go4retro/c-key/src/ps2.h

/*
    C=Key - Commodore <-> PS/2 Interface
    Copyright Jim Brain and RETRO Innovations, 2004-2012

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
    ps2.h: public functions and KEY definitions

*/

#ifndef PS2_H
#define PS2_H

typedef enum { PS2_MODE_DEVICE = 1, PS2_MODE_HOST = 2 } ps2mode_t;

#define PS2_KEY_UP            0xf0
#define PS2_KEY_EXT           0xe0
#define PS2_KEY_EXT_2         0xe1


// normal keys
#define PS2_KEY_F9            0x01
#define PS2_KEY_F5            0x03
#define PS2_KEY_F3            0x04
#define PS2_KEY_F1            0x05
#define PS2_KEY_F2            0x06
#define PS2_KEY_F12           0x07
#define PS2_KEY_F10           0x09
#define PS2_KEY_F8            0x0a
#define PS2_KEY_F6            0x0b
#define PS2_KEY_F4            0x0c
#define PS2_KEY_TAB           0x0d
#define PS2_KEY_BACKQUOTE     0x0e
#define PS2_KEY_ALT           0x11
#define PS2_KEY_LSHIFT        0x12
#define PS2_KEY_LCTRL         0x14
#define PS2_KEY_Q             0x15
#define PS2_KEY_1             0x16
#define PS2_KEY_Z             0x1a
#define PS2_KEY_S             0x1b
#define PS2_KEY_A             0x1c
#define PS2_KEY_W             0x1d
#define PS2_KEY_2             0x1e
#define PS2_KEY_C             0x21
#define PS2_KEY_X             0x22
#define PS2_KEY_D             0x23
#define PS2_KEY_E             0x24
#define PS2_KEY_4             0x25
#define PS2_KEY_3             0x26
#define PS2_KEY_SPACE         0x29
#define PS2_KEY_V             0x2a
#define PS2_KEY_F             0x2b
#define PS2_KEY_T             0x2c
#define PS2_KEY_R             0x2d
#define PS2_KEY_5             0x2e
#define PS2_KEY_N             0x31
#define PS2_KEY_B             0x32
#define PS2_KEY_H             0x33
#define PS2_KEY_G             0x34
#define PS2_KEY_Y             0x35
#define PS2_KEY_6             0x36
#define PS2_KEY_M             0x3a
#define PS2_KEY_J             0x3b
#define PS2_KEY_U             0x3c
#define PS2_KEY_7             0x3d
#define PS2_KEY_8             0x3e
#define PS2_KEY_COMMA         0x41
#define PS2_KEY_K             0x42
#define PS2_KEY_I             0x43
#define PS2_KEY_O             0x44
#define PS2_KEY_0             0x45
#define PS2_KEY_9             0x46
#define PS2_KEY_PERIOD        0x49
#define PS2_KEY_SLASH         0x4a
#define PS2_KEY_L             0x4b
#define PS2_KEY_SEMICOLON     0x4c
#define PS2_KEY_P             0x4d
#define PS2_KEY_MINUS         0x4e
#define PS2_KEY_APOSTROPHE    0x52
#define PS2_KEY_INT2          0x53
#define PS2_KEY_LBRACKET      0x54
#define PS2_KEY_EQUALS        0x55
#define PS2_KEY_CAPS_LOCK     0x58
#define PS2_KEY_RSHIFT        0x59
#define PS2_KEY_ENTER         0x5a
#define PS2_KEY_RBRACKET      0x5b
#define PS2_KEY_BACKSLASH     0x5d
#define PS2_KEY_INT1          0x61
#define PS2_KEY_BS            0x66
#define PS2_KEY_NUM_1         0x69
#define PS2_KEY_NUM_4         0x6b
#define PS2_KEY_NUM_7         0x6c
#define PS2_KEY_NUM_0         0x70
#define PS2_KEY_NUM_PERIOD    0x71
#define PS2_KEY_NUM_2         0x72
#define PS2_KEY_NUM_5         0x73
#define PS2_KEY_NUM_6         0x74
#define PS2_KEY_NUM_8         0x75
#define PS2_KEY_ESC           0x76
#define PS2_KEY_NUM_LOCK      0x77
#define PS2_KEY_F11           0x78
#define PS2_KEY_NUM_PLUS      0x79
#define PS2_KEY_NUM_3         0x7a
#define PS2_KEY_NUM_MINUS     0x7b
#define PS2_KEY_NUM_STAR      0x7c
#define PS2_KEY_NUM_9         0x7d
#define PS2_KEY_SCROLL_LOCK   0x7e
#define PS2_KEY_F7            0x83


// extended keys
#define PS2_KEY_RALT          0x11
#define PS2_KEY_ECTRL         0x12
#define PS2_KEY_RCTRL         0x14
#define PS2_KEY_NUM_SLASH     0x4a
#define PS2_KEY_NUM_ENTER     0x5a
#define PS2_KEY_END           0x69
#define PS2_KEY_CRSR_LEFT     0x6b
#define PS2_KEY_HOME          0x6c
#define PS2_KEY_INSERT        0x70
#define PS2_KEY_DELETE        0x71
#define PS2_KEY_CRSR_DOWN     0x72
#define PS2_KEY_CRSR_RIGHT    0x74
#define PS2_KEY_CRSR_UP       0x75
#define PS2_KEY_PAGE_DOWN     0x7a
#define PS2_KEY_PAGE_UP       0x7d

// significantly extended keys
// E012E07C
#define PS2_KEY_PRINT_SCREEN  0x7c
// E11477E1F014F077
#define PS2_KEY_PCTRL         0x14
#define PS2_KEY_PAUSE         0x77


#define PS2_CMD_LEDS          0xed
#define PS2_CMD_ECHO          0xee
#define PS2_CMD_SET_CODE_SET  0xf0
#define PS2_CMD_READ_ID       0xf2
#define PS2_CMD_SET_RATE      0xf3
#define PS2_CMD_ENABLE        0xf4
#define PS2_CMD_DISABLE       0xf5
#define PS2_CMD_DEFAULT       0xf6
#define PS2_CMD_RESEND        0xfe
#define PS2_CMD_RESET         0xff

#define PS2_CMD_ERROR         0x00
#define PS2_CMD_BAT           0xaa
#define PS2_CMD_ECHO_RESP     0xee
#define PS2_CMD_ACK           0xfa
#define PS2_CMD_BAT_FAILURE   0xfc
#define PS2_CMD_OVERFLOW      0xff

#define PS2_LED_SCROLL_LOCK   (1 << 0)
#define PS2_LED_NUM_LOCK      (1 << 1)
#define PS2_LED_CAPS_LOCK     (1 << 2)

#define PS2_MS_CMD_RESET      PS2_CMD_RESET
#define PS2_MS_CMD_RESEND     PS2_CMD_RESEND
#define PS2_MS_CMD_ACK        PS2_CMD_ACK
#define PS2_MS_CMD_REPORT     0xf4
#define PS2_MS_CMD_REPORTOFF  0xf5
#define PS2_MS_CMD_SET_SAMPLE 0xf3
#define PS2_MS_CMD_READ_ID    PS2_CMD_READ_ID
#define PS2_MS_CMD_READ_DATA  0xeb

#define PS2_RX_BUFFER_MASK   (_BV(PS2_RX_BUFFER_SHIFT) - 1)
#define PS2_TX_BUFFER_MASK   (_BV(PS2_TX_BUFFER_SHIFT) - 1)
/*
 * After a device sends a byte to host, it has to holdoff for a while
 * before doing anything else.  One KB I tested this is 2.14mS.
 */

/* PS2 Clock INT */
#if defined __AVR_ATmega8__ ||  defined __AVR_ATmega16__ || defined __AVR_ATmega32__ || defined __AVR_ATmega162__
#  define CLK_INTDR     MCUCR     // INT Direction Register
#  define CLK_INTCR     GICR      // INT Control Register
#  define CLK_INTFR     GIFR      // INT Flag Register
#  if PS2_CLK_PIN == _BV(PD3)
#    define CLK_ISC0      ISC10
#    define CLK_ISC1      ISC11
#    define CLK_INT       INT1
#    define CLK_INTF      INTF1
#    define CLK_INT_vect  INT1_vect
#  elif PS2_CLK_PIN == _BV(PD2)
#    define CLK_ISC0      ISC00
#    define CLK_ISC1      ISC01
#    define CLK_INT       INT0
#    define CLK_INTF      INTF0
#    define CLK_INT_vect  INT0_vect
#  else
#    error "Please define CLK INT Settings"
#  endif
#else
#  define CLK_INTDR     EICRA     // INT Direction Register
#  define CLK_INTCR     EIMSK     // INT Control Register
#  define CLK_INTFR     EIFR      // INT Flag Register
#  if PS2_CLK_PIN == _BV(PD3)
#    define CLK_ISC0      ISC10
#    define CLK_ISC1      ISC11
#    define CLK_INT       INT1
#    define CLK_INTF      INTF1
#    define CLK_INT_vect  INT1_vect
#  else
#    define CLK_ISC0      ISC00
#    define CLK_ISC1      ISC01
#    define CLK_INT       INT0
#    define CLK_INTF      INTF0
#    define CLK_INT_vect  INT0_vect
#  endif
#endif

/* PS2 Timer */
#if defined __AVR_ATmega8__

#  define PS2_TIMER_COMP_vect   TIMER2_COMP_vect
#  define PS2_OCR               OCR2
#  define PS2_TCNT              TCNT2
#  define PS2_TCCR1             TCCR2
#  define PS2_TCCR1_DATA        _BV(CS21)
#  define PS2_TCCR2             TCCR2
#  define PS2_TCCR2_DATA        _BV(WGM21)
#  define PS2_TIFR              TIFR
#  define PS2_TIFR_DATA         _BV(OCF2)
#  define PS2_TIMSK             TIMSK
#  define PS2_TIMSK_DATA        _BV(OCIE2)

#elif defined __AVR_ATmega28__ || defined __AVR_ATmega48__ || defined __AVR_ATmega88__ || defined __AVR_ATmega168__

#  define PS2_TIMER_COMP_vect   TIMER2_COMPA_vect
#  define PS2_OCR               OCR2A
#  define PS2_TCNT              TCNT2
#  define PS2_TCCR1             TCCR2B
#  define PS2_TCCR1_DATA        _BV(CS21)
#  define PS2_TCCR2             TCCR2A
#  define PS2_TCCR2_DATA        _BV(WGM21)
#  define PS2_TIFR              TIFR2
#  define PS2_TIFR_DATA         _BV(OCF2A)
#  define PS2_TIMSK             TIMSK2
#  define PS2_TIMSK_DATA        _BV(OCIE2A)

#elif defined __AVR_ATmega16__ || defined __AVR_ATmega32__ || defined __AVR_ATmega162__

#  define PS2_TIMER_COMP_vect   TIMER0_COMP_vect
#  define PS2_OCR               OCR0
#  define PS2_TCNT              TCNT0
#  define PS2_TCCR1             TCCR0
#  define PS2_TCCR1_DATA        _BV(CS01)
#  define PS2_TCCR2             TCCR0
#  define PS2_TCCR2_DATA        _BV(WGM01)
#  define PS2_TIFR              TIFR
#  define PS2_TIFR_DATA         _BV(OCF0)
#  define PS2_TIMSK             TIMSK
#  define PS2_TIMSK_DATA        _BV(OCIE0)

#else
#  error Unknown chip!
#endif



#define PS2_HALF_CYCLE 36
#define PS2_SEND_HOLDOFF_COUNT  ((uint8_t)(2140/PS2_HALF_CYCLE))

typedef enum {PS2_ST_IDLE
             ,PS2_ST_PREP_START
             ,PS2_ST_SEND_START
             ,PS2_ST_PREP_BIT
             ,PS2_ST_SEND_BIT
             ,PS2_ST_PREP_PARITY
             ,PS2_ST_SEND_PARITY
             ,PS2_ST_PREP_STOP
             ,PS2_ST_SEND_STOP
             ,PS2_ST_HOLDOFF
             ,PS2_ST_WAIT_START
             ,PS2_ST_GET_START
             ,PS2_ST_WAIT_BIT
             ,PS2_ST_GET_BIT
             ,PS2_ST_WAIT_PARITY
             ,PS2_ST_GET_PARITY
             ,PS2_ST_WAIT_STOP
             ,PS2_ST_GET_STOP
             ,PS2_ST_GET_ACK
             ,PS2_ST_WAIT_ACK
             ,PS2_ST_WAIT_ACK2
             ,PS2_ST_HOST_INHIBIT
             ,PS2_ST_WAIT_RESPONSE
             } ps2state_t;

static inline __attribute__((always_inline)) void ps2_init_timer(void) {
  // set prescaler to System Clock/8
  PS2_TCCR1 |= PS2_TCCR1_DATA;
  // CTC mode
  PS2_TCCR2 |= PS2_TCCR2_DATA;
}

static inline __attribute__((always_inline)) void ps2_set_clk(void) {
  PS2_CLK_OUT |= PS2_CLK_PIN;
  PS2_CLK_DDR &= (uint8_t)~PS2_CLK_PIN;
}

static inline __attribute__((always_inline)) void ps2_clear_clk(void) {
  PS2_CLK_DDR |= PS2_CLK_PIN;
  PS2_CLK_OUT &= (uint8_t)~PS2_CLK_PIN;
}

static inline __attribute__((always_inline)) uint8_t ps2_read_clk(void) {
  return PS2_CLK_IN & PS2_CLK_PIN;
}

static inline __attribute__((always_inline)) void ps2_set_data(void) {
  PS2_DATA_OUT |= PS2_DATA_PIN;
  PS2_DATA_DDR &= (uint8_t)~PS2_DATA_PIN;
}

static inline __attribute__((always_inline)) void ps2_clear_data(void) {
  PS2_DATA_DDR |= PS2_DATA_PIN;
  PS2_DATA_OUT &= (uint8_t)~PS2_DATA_PIN;
}

static inline __attribute__((always_inline)) uint8_t ps2_read_data(void) {
  return PS2_DATA_IN & PS2_DATA_PIN;
}

#if defined PS2_ENABLE_HOST && defined PS2_ENABLE_DEVICE
#define PS2_CALL(dev,host) \
  switch(ps2_mode) {\
  case PS2_MODE_DEVICE: \
    dev; \
    break; \
  case PS2_MODE_HOST: \
    host; \
    break; \
  }
#else
#  if defined PS2_ENABLE_DEVICE
#    define PS2_CALL(dev,host) dev
#  else
#    define PS2_CALL(dev,host) host
#  endif
#endif

void ps2_init(ps2mode_t mode);
uint8_t ps2_getc(void);
void ps2_putc(uint8_t data);
uint8_t ps2_data_available(void);
void ps2_handle_cmds(uint8_t data);
uint16_t ps2_get_typematic_delay(uint8_t rate);
uint16_t ps2_get_typematic_period(uint8_t rate);
void ps2_clear_buffers(void);

// Add 1 and multiply by 250ms to get time
#define PS2_GET_DELAY(rate)   ((rate & 0x60) >> 5)
// Multiply by 4.17 to get CPS (or << 2)
#define PS2_GET_RATE(rate)    ((8 + (rate & 0x07)) * (1 << ((rate & 0x18) >> 3)))
#define CALC_RATE(delay,rate) ((rate & 0x1f) + ((delay & 0x03) << 5))

#endif
