go4retro/c-key/reference/ps2-to-cbm/source/reg-18f4520.h

#BYTE PORTA		=0xF80

#BYTE PORTB		=0xF81

#BYTE PORTC		=0xF82

#BYTE PORTD		=0xF83

#BYTE PORTE		=0xF84

#BYTE LATD		=0xF8C

#BYTE TRISA		=0xF92

#BYTE TRISB		=0xF93

#BYTE TRISC		=0xF94

#BYTE TRISD		=0xF95

#BYTE TRISE		=0xF96

#BYTE OSCTUNE	=0xF9B

#BYTE PIR1 		=0xF9E
#BIT  RCIF		=PIR1.5
#BIT  SSPIF		=PIR1.3
#BIT  CCP1IF	=PIR1.2
#BIT  TMR2IF	=PIR1.1
#BIT  TMR1IF	=PIR1.0

#BYTE PIR2		=0xFA1
#BIT  CCP2IF	=PIR2.0

#BYTE RCSTA		=0xFAB
#BIT  OERR		=RCSTA.1
#BIT  FERR		=RCSTA.2
#BIT  CREN		=RCSTA.4

#BYTE TXSTA		=0xFAC
#BIT  BRGH		=TXSTA.2
#BIT  TXEN		=TXSTA.5

#BYTE RCREG		=0xFAE

#BYTE SPBRG		=0xFAF

#BYTE CVRCON	=0xFB5

#BYTE CCP1CON	=0xFBD
#BIT  CCP1X		=CCP1CON.5
#BIT  CCP1Y		=CCP1CON.4

#BYTE CCPR1L	=0xFBE

#BYTE SSPCON1	=0xFC6
#BIT  CKP		=SSPCON1.4
#BIT  SSPEN		=SSPCON1.5

#BYTE SSPSTAT	=0xFC7
#BIT  BF		=SSPSTAT.0

#BYTE SSPBUF	=0xFC9

#BYTE OSCCON	=0xFD3

#BYTE FSR2H		=0xFDA

#BYTE FSR2L		=0xFD9

#BYTE BSR		=0xFE0

#BYTE INDF0		=0xFEF

#BYTE FSR0H		=0xFEA

#BYTE FSR0L		=0xFE9

#BYTE INTCON3	=0xFF0
#BIT  INT1IF	=INTCON3.0
#BIT  INT2IF	=INTCON3.1
#BIT  INT1IE	=INTCON3.3
#BIT  INT2IE	=INTCON3.4
#BIT  INT1IP	=INTCON3.6
#BIT  INT2IP	=INTCON3.7

#BYTE INTCON	=0xFF2
#BIT  INT0IF	=INTCON.1
